janelia-experimental-technology/FlySong/miniFlySong/miniFlySong Rig.jpg

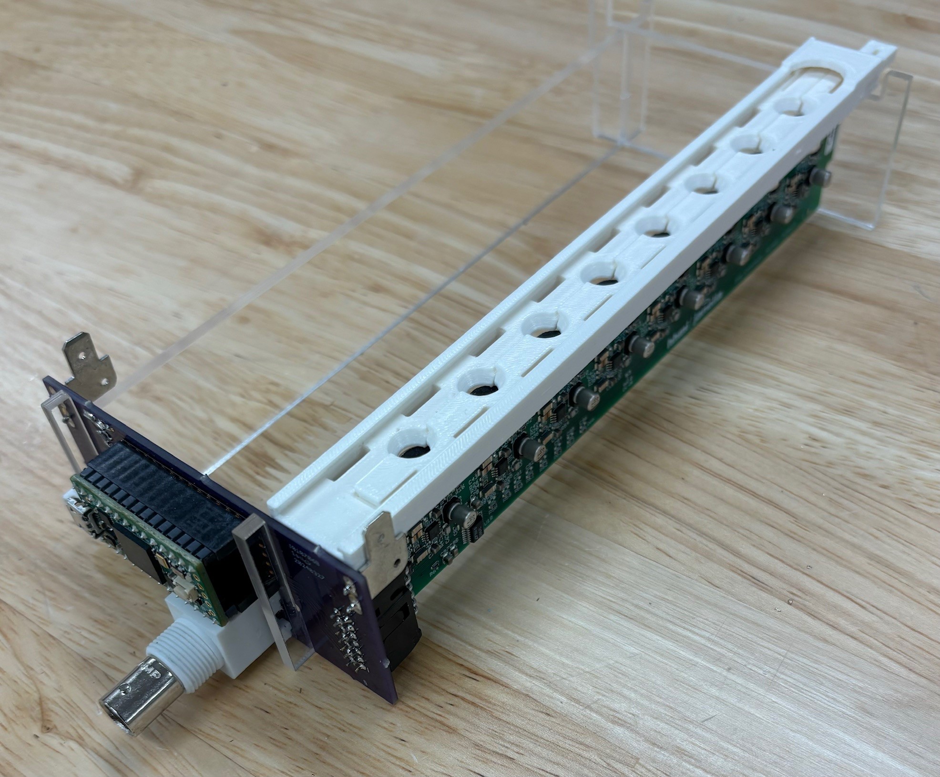
miniFlySong/miniFlySong Rig.jpg
