janelia-experimental-technology/FlySong/PHOTOS/camera cables.jpg

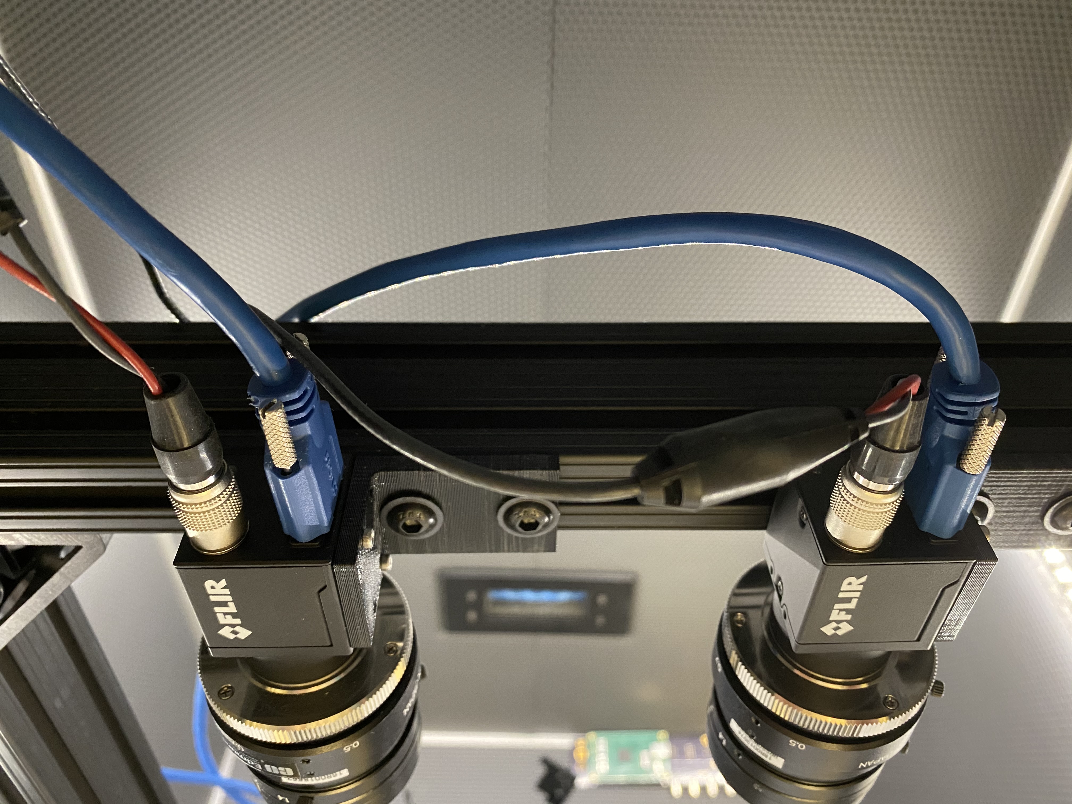
PHOTOS/camera cables.jpg
