janelia-experimental-technology/FlySong/PHOTOS/cameras and mount.jpg

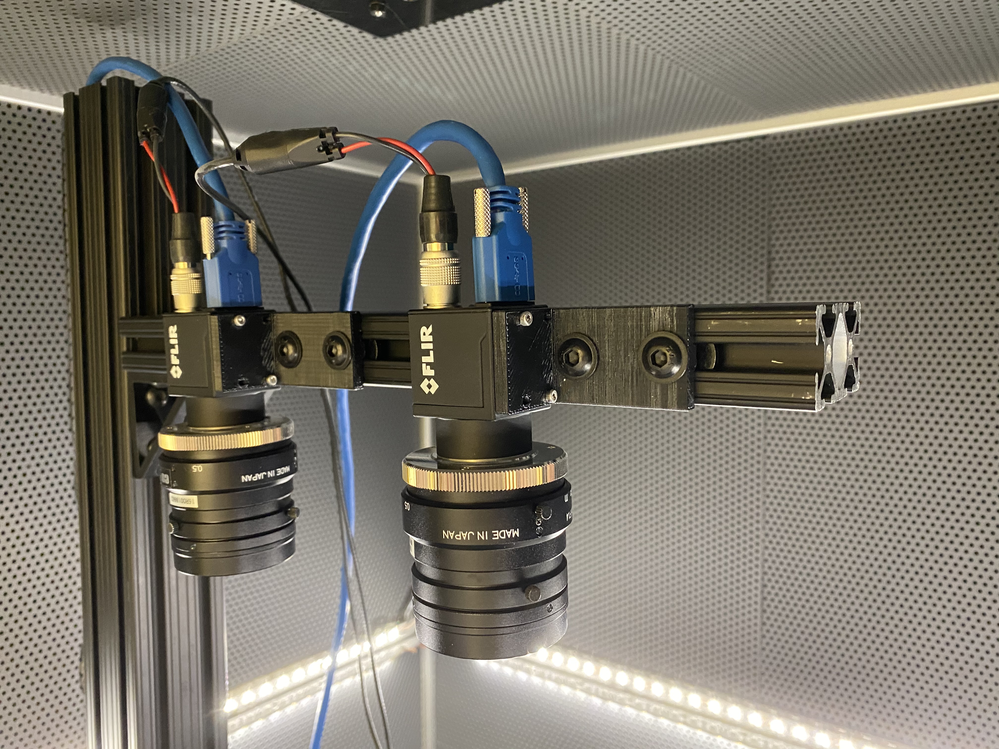
PHOTOS/cameras and mount.jpg
