janelia-experimental-technology/FlySong/PHOTOS/cameras.jpg

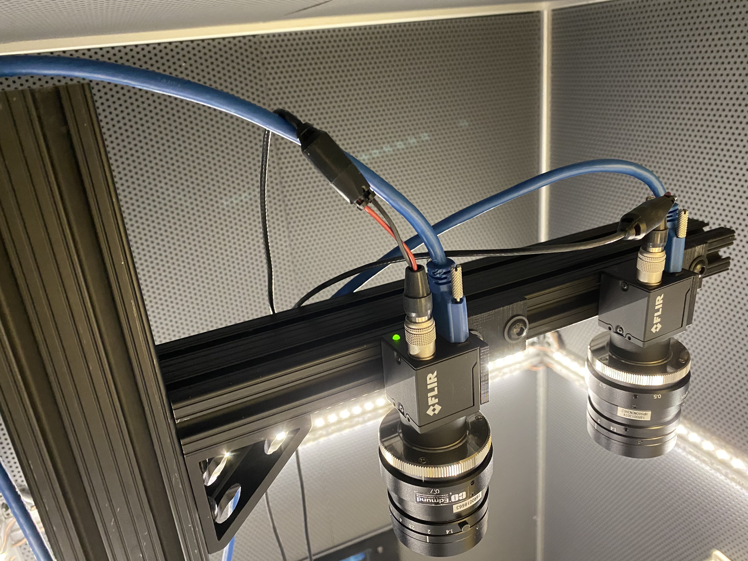
PHOTOS/cameras.jpg
