janelia-experimental-technology/FlySong/PHOTOS/RIG WITH RGB/Drigwithfrontmirror.jpg

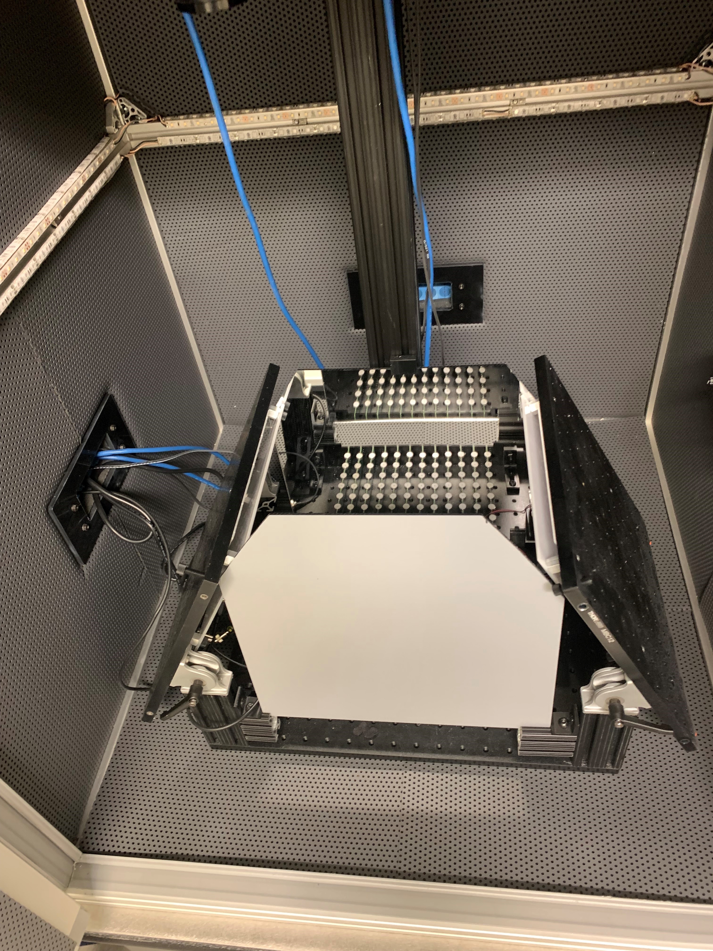
PHOTOS/RIG WITH RGB/Drigwithfrontmirror.jpg
