janelia-experimental-technology/FlySong/PHOTOS/RIG WITH RGB/LEDrigbehind.jpg

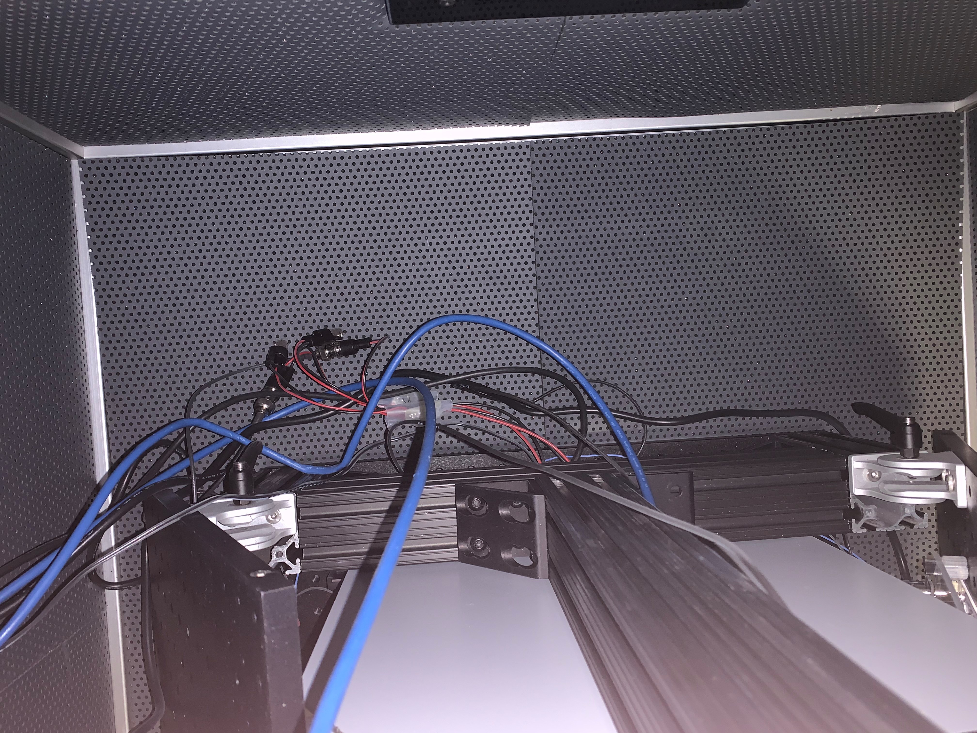
PHOTOS/RIG WITH RGB/LEDrigbehind.jpg
