janelia-experimental-technology/FlySong/PHOTOS/RIG WITH RGB/LEDrigtop2.jpg

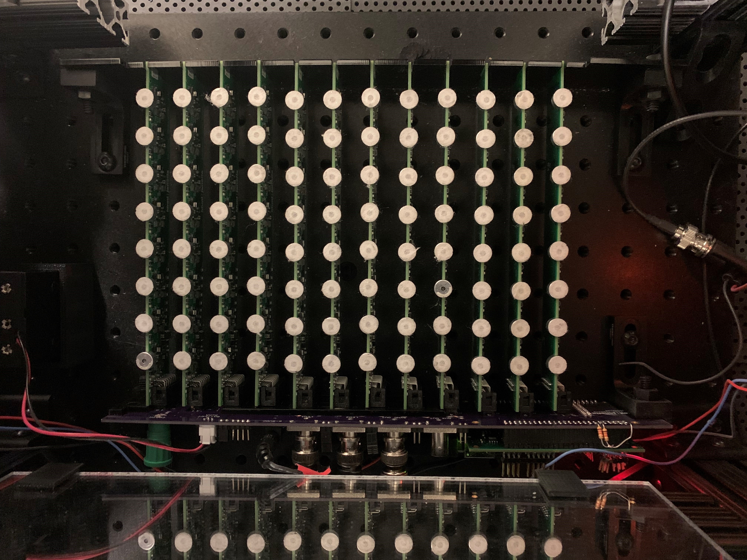
PHOTOS/RIG WITH RGB/LEDrigtop2.jpg
