janelia-experimental-technology/FlySong/PHOTOS/RIG WITH RGB/LEDrigtop.jpg

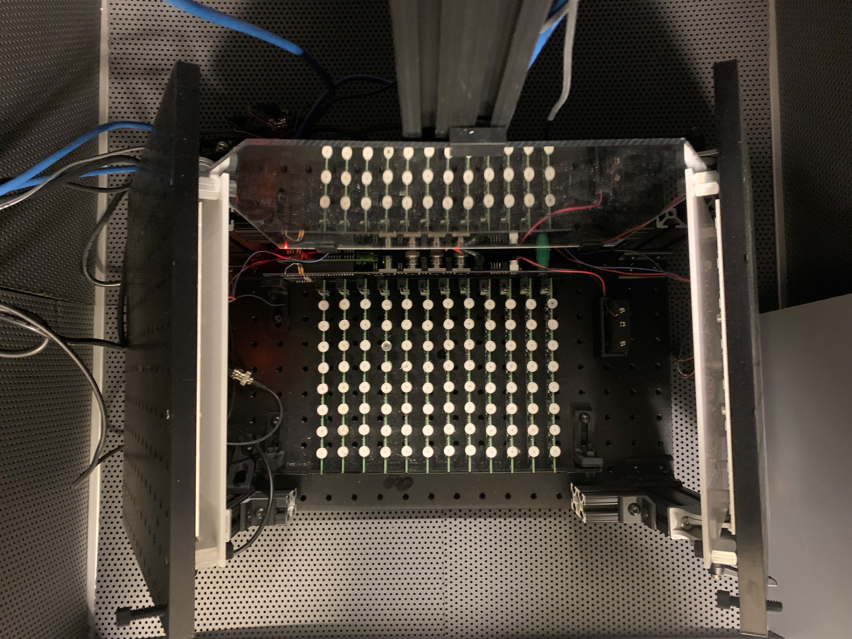
PHOTOS/RIG WITH RGB/LEDrigtop.jpg
