janelia-experimental-technology/FlySong/PHOTOS/Single mic board.JPG

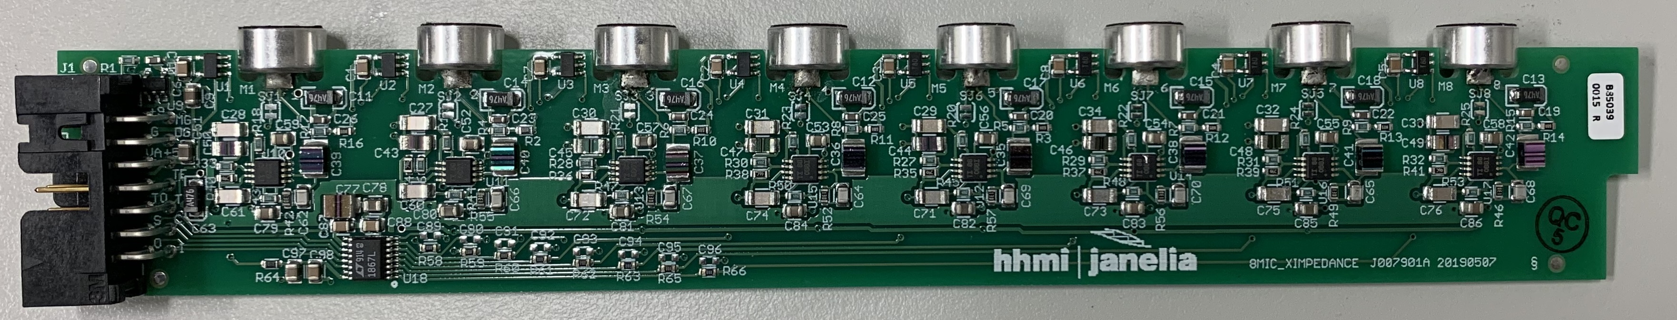
PHOTOS/Single mic board.JPG
