janelia-experimental-technology/FlySong/Mechanical/LaserCuts/ChamberSupports_LaserCuts_J008340A.dxf

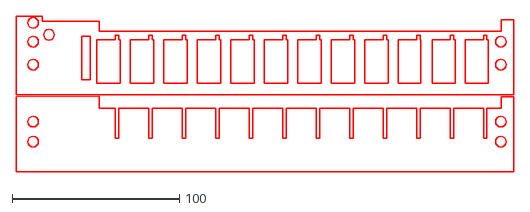
[picture p31: CAD file, 2023-11-08]
Mechanical/LaserCuts/ChamberSupports_LaserCuts_J008340A.dxf
297.0 x 93.0
