janelia-experimental-technology/FlySong/Electrical/TriggerCable.pdf

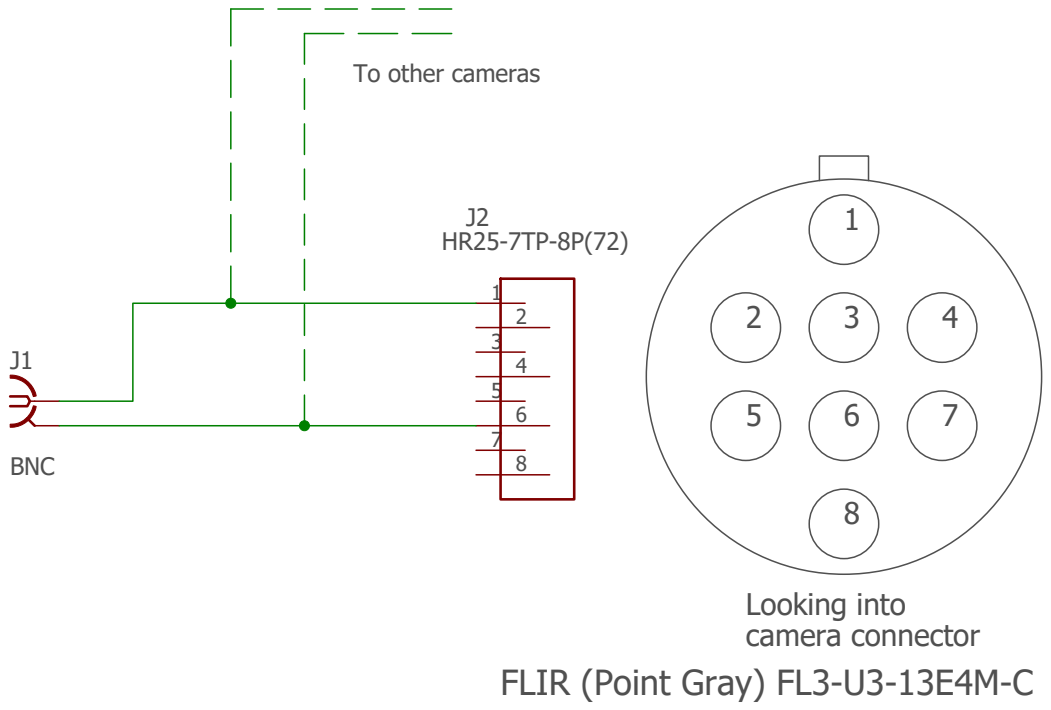
[picture p32: page 1]
Looking into camera connector; BNC; Date: not saved!; Sheet: 1/1; REV:; TITLE:; Document Number:; TriggerCable

To other cameras

FLIR (Point Gray) FL3-U3-13E4M-C
