janelia-experimental-technology/FlySong/FPGAsource/FPGAwSRAM/FPGAwSRAM.srcs/sources_1/imports/96mic/okBTPipeIn.v

// Copyright 1986-2015 Xilinx, Inc. All Rights Reserved.
// --------------------------------------------------------------------------------
// Tool Version: Vivado v.2015.1 (win64) Build 1215546 Mon Apr 27 19:22:08 MDT 2015
// Date        : Mon Mar 14 14:44:02 2016
// Host        : ENG001 running 64-bit major release  (build 9200)
// Command     : write_verilog encrypted/okBTPipeIn.v -force
// Design      : okBTPipeIn
// Purpose     : This is a Verilog netlist of the current design or from a specific cell of the design. The output is an
//               IEEE 1364-2001 compliant Verilog HDL file that contains netlist information obtained from the input
//               design files.
// Device      : xc7a15tftg256-1
// --------------------------------------------------------------------------------
`timescale 1 ps / 1 ps
`pragma protect begin_protected
`pragma protect version = 1
`pragma protect encrypt_agent = "XILINX"
`pragma protect encrypt_agent_info = "Xilinx Encryption Tool 2014"
`pragma protect key_keyowner = "Xilinx", key_keyname= "xilinx_rsa_key", key_method = "rsa"
`pragma protect encoding = (enctype = "BASE64", line_length = 76, bytes = 256)
`pragma protect key_block
Fh4uwRzu/dnt5r1QK762rHFgJkB9yfB/yrZYcW5Xy1imGTabUug4dFeSXXOdPlOcM7rrzuRp/h0H
xBfA3tb1mhHGhxead6KLwcbITD29SkVixk7EAfrhfXsD7AJevRaIbT9SvUi80ju3tSvxARpVkpB9
lUH7NHTmvPrGc9fxVg5305HHPtw7yxeQ5QIUJT7Pp70OrIjOF14pLfanrSt3Sp5aoSveh1QaKLCC
TkiL7rNUEZyYnwcvnaIB3q99gLVUxVYKGOKqI85L7sqMW/h4TQZ/COntCu+Ya/B+OVFPVO0xWF26
eNhhSwdBffT30fBPmPcC9+IbmshED+ESR4J4xw==

`pragma protect data_method = "AES128-CBC"
`pragma protect encoding = (enctype = "BASE64", line_length = 76, bytes = 5392)
`pragma protect data_block
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
`pragma protect end_protected
