janelia-experimental-technology/FlySong/FPGAsource/FPGAwSRAM/FPGAwSRAM.srcs/sources_1/imports/96mic/okBTPipeOut.v

// Copyright 1986-2015 Xilinx, Inc. All Rights Reserved.
// --------------------------------------------------------------------------------
// Tool Version: Vivado v.2015.1 (win64) Build 1215546 Mon Apr 27 19:22:08 MDT 2015
// Date        : Mon Mar 14 14:44:09 2016
// Host        : ENG001 running 64-bit major release  (build 9200)
// Command     : write_verilog encrypted/okBTPipeOut.v -force
// Design      : okBTPipeOut
// Purpose     : This is a Verilog netlist of the current design or from a specific cell of the design. The output is an
//               IEEE 1364-2001 compliant Verilog HDL file that contains netlist information obtained from the input
//               design files.
// Device      : xc7a15tftg256-1
// --------------------------------------------------------------------------------
`timescale 1 ps / 1 ps
`pragma protect begin_protected
`pragma protect version = 1
`pragma protect encrypt_agent = "XILINX"
`pragma protect encrypt_agent_info = "Xilinx Encryption Tool 2014"
`pragma protect key_keyowner = "Xilinx", key_keyname= "xilinx_rsa_key", key_method = "rsa"
`pragma protect encoding = (enctype = "BASE64", line_length = 76, bytes = 256)
`pragma protect key_block
ceNoom6rbxBo+aYj+vBCbk7ZTXtGGbR1PNspMmEgzM12jxUhxhG8qXBXLPctP1Fa2NEXUIKIj4sh
Lmk7Nztbh1N6vVtappy26EiW4+ZoatkzdjAM5lZ5qNvalbiQNZPtWkysVhgkzsw+Dp858GLCppmi
96nc9nbWnJmwm5MVFI5jCu1HGCWIx/ghrDwHuIKqzORi1j1ZawqX2oKo0zJgWOreHumBSc8EhQHg
zt+WDYfpjdkIg/9/9+zmKAe8qIX0/IW1a2M/NPYptsqt0FcJzw/kCYaHBI710mXWGc9dgOKZqzsU
7VkZgweg8jSlaVgsCk0Rwtsa72uSkHqy9gIMng==

`pragma protect data_method = "AES128-CBC"
`pragma protect encoding = (enctype = "BASE64", line_length = 76, bytes = 5536)
`pragma protect data_block
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
jU1PiOcMdw==
`pragma protect end_protected
