janelia-experimental-technology/FlySong/FPGAsource/FPGAwSRAM/FPGAwSRAM.srcs/sources_1/imports/96mic/okWireIn.v

// Copyright 1986-2015 Xilinx, Inc. All Rights Reserved.
// --------------------------------------------------------------------------------
// Tool Version: Vivado v.2015.1 (win64) Build 1215546 Mon Apr 27 19:22:08 MDT 2015
// Date        : Mon Mar 14 14:44:37 2016
// Host        : ENG001 running 64-bit major release  (build 9200)
// Command     : write_verilog encrypted/okWireIn.v -force
// Design      : okWireIn
// Purpose     : This is a Verilog netlist of the current design or from a specific cell of the design. The output is an
//               IEEE 1364-2001 compliant Verilog HDL file that contains netlist information obtained from the input
//               design files.
// Device      : xc7a15tftg256-1
// --------------------------------------------------------------------------------
`timescale 1 ps / 1 ps
`pragma protect begin_protected
`pragma protect version = 1
`pragma protect encrypt_agent = "XILINX"
`pragma protect encrypt_agent_info = "Xilinx Encryption Tool 2014"
`pragma protect key_keyowner = "Xilinx", key_keyname= "xilinx_rsa_key", key_method = "rsa"
`pragma protect encoding = (enctype = "BASE64", line_length = 76, bytes = 256)
`pragma protect key_block
He7n+UnxRlqTMnbJBcvT+3Ny8AGCD7760dxFaGgSg6jzVUlvq3/qnky7S4Cd0uXEhExU9A/G/+jV
swbCJDNCJwODO/1EqRvnPjltjimub9iz1Rq6a6vzJW6LPC6FEMTQgqMVCWjS6LJ6SVMqL0UyoaQ9
mJKnjG3gI8pImYNv0nE6eXMlkPftPxMJrk4+rkDeZ9FqTpFV0Z3isBoDvDqWVgWyZ18B3afR37E+
UQ2zCmuS6W7EVIW3SkF+OUdjV+bZebcOUz6w5B1g7iSEbGy5MXDnqL2yVPUtmJeCjpq6eEYTkNLz
hUoXTe+vTRjOGO54XuR7F+5prIaDBwPDYvPaow==

`pragma protect data_method = "AES128-CBC"
`pragma protect encoding = (enctype = "BASE64", line_length = 76, bytes = 6432)
`pragma protect data_block
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
`pragma protect end_protected
