janelia-experimental-technology/FlySong/FPGAsource/FPGAwSRAM/FPGAwSRAM.srcs/sources_1/imports/96mic/okWireOut.v

// Copyright 1986-2015 Xilinx, Inc. All Rights Reserved.
// --------------------------------------------------------------------------------
// Tool Version: Vivado v.2015.1 (win64) Build 1215546 Mon Apr 27 19:22:08 MDT 2015
// Date        : Mon Mar 14 14:44:42 2016
// Host        : ENG001 running 64-bit major release  (build 9200)
// Command     : write_verilog encrypted/okWireOut.v -force
// Design      : okWireOut
// Purpose     : This is a Verilog netlist of the current design or from a specific cell of the design. The output is an
//               IEEE 1364-2001 compliant Verilog HDL file that contains netlist information obtained from the input
//               design files.
// Device      : xc7a15tftg256-1
// --------------------------------------------------------------------------------
`timescale 1 ps / 1 ps
`pragma protect begin_protected
`pragma protect version = 1
`pragma protect encrypt_agent = "XILINX"
`pragma protect encrypt_agent_info = "Xilinx Encryption Tool 2014"
`pragma protect key_keyowner = "Xilinx", key_keyname= "xilinx_rsa_key", key_method = "rsa"
`pragma protect encoding = (enctype = "BASE64", line_length = 76, bytes = 256)
`pragma protect key_block
GboD47aqS2xv7i+Mjs8w+c63W4jbrSMpvLNoYOUUPcw50pbawmT7ps6S/S+g/cNI58UlBlEwAhK+
Sx8hgtqBs2+CmGYano4VyTPCSOqxhMlZyD30jkmOnLEsLR1ohXVEG1MTq1i9gegkzCn3vler0AEI
fUjtMy9CUX/hyDeYu13k7a/5+pmBYDl36X6wqfOnrReti4ec2RCOsUijL1nqEvBkIYPvCQ8H3fgh
JNvdqz3dfRVaCAJR0bVbRj0W6pX6Rpyt5IuMZQDwBusYJdi9ITpmQrkOWyst0UhkvwzftG4AZWUk
JdzQSXtuBW/FiY+xsNkyG4v9nht3/ebLZBd5pw==

`pragma protect data_method = "AES128-CBC"
`pragma protect encoding = (enctype = "BASE64", line_length = 76, bytes = 7312)
`pragma protect data_block
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
nPi3865pbc2lOAc/o1ByMg==
`pragma protect end_protected
