janelia-experimental-technology/FlySong/FPGAsource/FPGAwSRAM/FPGAwSRAM.srcs/sources_1/imports/96mic/okPipeIn.v

// Copyright 1986-2015 Xilinx, Inc. All Rights Reserved.
// --------------------------------------------------------------------------------
// Tool Version: Vivado v.2015.1 (win64) Build 1215546 Mon Apr 27 19:22:08 MDT 2015
// Date        : Mon Mar 14 14:44:14 2016
// Host        : ENG001 running 64-bit major release  (build 9200)
// Command     : write_verilog encrypted/okPipeIn.v -force
// Design      : okPipeIn
// Purpose     : This is a Verilog netlist of the current design or from a specific cell of the design. The output is an
//               IEEE 1364-2001 compliant Verilog HDL file that contains netlist information obtained from the input
//               design files.
// Device      : xc7a15tftg256-1
// --------------------------------------------------------------------------------
`timescale 1 ps / 1 ps
`pragma protect begin_protected
`pragma protect version = 1
`pragma protect encrypt_agent = "XILINX"
`pragma protect encrypt_agent_info = "Xilinx Encryption Tool 2014"
`pragma protect key_keyowner = "Xilinx", key_keyname= "xilinx_rsa_key", key_method = "rsa"
`pragma protect encoding = (enctype = "BASE64", line_length = 76, bytes = 256)
`pragma protect key_block
pp8uegFR+HcuxO82qfOr/bnWbU4BhkaXkdLwH8kbdE8cu3OBB891qpwMdlxpvV5KDxcGkOC8xI/2
yNy2IJ7eNr5S63N6x7KBeUN9nIWkN0+dvoPAUmtxsJJoLDsxoXaWtQ4/IgyaOjxGWN6gyyeIDGrU
1cCZfWLVN4PrGTT/yPVN+qkrLAM5fl4r45IIvLfLcIgTlLmg++MvKfiQiGMb1EWrXBI44qlEK90J
ciomIXwNng8LNQpz8hEPLRzbMAh2QkQs/O+8VBsz8lPHCuIh1Q07/nGMN1V7noRKYraVMqKKY4C4
T+oO5eQox+KOT7l24IIg/glWMKQTSW2mFGHPIA==

`pragma protect data_method = "AES128-CBC"
`pragma protect encoding = (enctype = "BASE64", line_length = 76, bytes = 5328)
`pragma protect data_block
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
GgHhEjmCwbM9kBYY49kCXhUT7aydmYbmcKWH
`pragma protect end_protected
