janelia-experimental-technology/FlySong/FPGAsource/FPGAwSRAM/FPGAwSRAM.srcs/sources_1/imports/96mic/okPipeOut.v

// Copyright 1986-2015 Xilinx, Inc. All Rights Reserved.
// --------------------------------------------------------------------------------
// Tool Version: Vivado v.2015.1 (win64) Build 1215546 Mon Apr 27 19:22:08 MDT 2015
// Date        : Mon Mar 14 14:44:20 2016
// Host        : ENG001 running 64-bit major release  (build 9200)
// Command     : write_verilog encrypted/okPipeOut.v -force
// Design      : okPipeOut
// Purpose     : This is a Verilog netlist of the current design or from a specific cell of the design. The output is an
//               IEEE 1364-2001 compliant Verilog HDL file that contains netlist information obtained from the input
//               design files.
// Device      : xc7a15tftg256-1
// --------------------------------------------------------------------------------
`timescale 1 ps / 1 ps
`pragma protect begin_protected
`pragma protect version = 1
`pragma protect encrypt_agent = "XILINX"
`pragma protect encrypt_agent_info = "Xilinx Encryption Tool 2014"
`pragma protect key_keyowner = "Xilinx", key_keyname= "xilinx_rsa_key", key_method = "rsa"
`pragma protect encoding = (enctype = "BASE64", line_length = 76, bytes = 256)
`pragma protect key_block
BsgjUAD1O8euvel2hbkc8te3elD8HtfBgAa/XrN2xeB4rmm7DSoyeXS7/2h3a5ISqn9xaWsTo34h
6ck4zlRUcANFHBE36Xael0QoKT0daD75NywGKJIlfdfcsdZKJtPPEIldq0FoRchDVK1zKBIiD75I
3qChKLhP5L/AFR94uIm7hYtUpP0WqRznH39JVAd4cqw62go1rKzbpY8ZdBWE3UNPiBGsLxv5KSGj
NnaTXdPe6cxQgYOdlAtetth9hKQe7eGvcKOSGFE03r1zPMe3xlX4PIDCqFE/+adAgG0R84cW+xgS
fgf8NICXgJ64PibA/IK8HKZ6+rSC9EmyGeb36A==

`pragma protect data_method = "AES128-CBC"
`pragma protect encoding = (enctype = "BASE64", line_length = 76, bytes = 5232)
`pragma protect data_block
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
`pragma protect end_protected
