janelia-experimental-technology/FlySong/FPGAsource/FPGAwSRAM/.Xil/FPGAwSRAM.ip_user_files/ip/mult_gen_0/mult_gen_0_stub.v

// Copyright 1986-2017 Xilinx, Inc. All Rights Reserved.
// --------------------------------------------------------------------------------
// Tool Version: Vivado v.2017.1 (win64) Build 1846317 Fri Apr 14 18:55:03 MDT 2017
// Date        : Sun May 14 15:34:09 2017
// Host        : sawtelles-lw1 running 64-bit major release  (build 9200)
// Command     : write_verilog -force -mode synth_stub
//               C:/PROJECTS/STERN/96CH_RECORDER/FPGA/96mic/96mic.runs/mult_gen_0_synth_1/mult_gen_0_stub.v
// Design      : mult_gen_0
// Purpose     : Stub declaration of top-level module interface
// Device      : xc7a15tftg256-1
// --------------------------------------------------------------------------------

// This empty module with port declaration file causes synthesis tools to infer a black box for IP.
// The synthesis directives are for Synopsys Synplify support to prevent IO buffer insertion.
// Please paste the declaration into a Verilog source file or add the file as an additional source.
(* x_core_info = "mult_gen_v12_0_12,Vivado 2017.1" *)
module mult_gen_0(CLK, A, P)
/* synthesis syn_black_box black_box_pad_pin="CLK,A[15:0],P[32:0]" */;
  input CLK;
  input [15:0]A;
  output [32:0]P;
endmodule
