janelia-experimental-technology/FlySong/FPGAsource/FPGAwSRAM/.Xil/FPGAwSRAM.ip_user_files/ip/mult_gen_0/mult_gen_0_stub.vhdl

-- Copyright 1986-2017 Xilinx, Inc. All Rights Reserved.
-- --------------------------------------------------------------------------------
-- Tool Version: Vivado v.2017.1 (win64) Build 1846317 Fri Apr 14 18:55:03 MDT 2017
-- Date        : Sun May 14 15:34:09 2017
-- Host        : sawtelles-lw1 running 64-bit major release  (build 9200)
-- Command     : write_vhdl -force -mode synth_stub
--               C:/PROJECTS/STERN/96CH_RECORDER/FPGA/96mic/96mic.runs/mult_gen_0_synth_1/mult_gen_0_stub.vhdl
-- Design      : mult_gen_0
-- Purpose     : Stub declaration of top-level module interface
-- Device      : xc7a15tftg256-1
-- --------------------------------------------------------------------------------
library IEEE;
use IEEE.STD_LOGIC_1164.ALL;

entity mult_gen_0 is
  Port ( 
    CLK : in STD_LOGIC;
    A : in STD_LOGIC_VECTOR ( 15 downto 0 );
    P : out STD_LOGIC_VECTOR ( 32 downto 0 )
  );

end mult_gen_0;

architecture stub of mult_gen_0 is
attribute syn_black_box : boolean;
attribute black_box_pad_pin : string;
attribute syn_black_box of stub : architecture is true;
attribute black_box_pad_pin of stub : architecture is "CLK,A[15:0],P[32:0]";
attribute x_core_info : string;
attribute x_core_info of stub : architecture is "mult_gen_v12_0_12,Vivado 2017.1";
begin
end;
