janelia-experimental-technology/FlySong/FPGAsource/FPGAwSRAM/.Xil/FPGAwSRAM.ip_user_files/ip/mult_gen_0/mult_gen_0_sim_netlist.v

// Copyright 1986-2017 Xilinx, Inc. All Rights Reserved.
// --------------------------------------------------------------------------------
// Tool Version: Vivado v.2017.1 (win64) Build 1846317 Fri Apr 14 18:55:03 MDT 2017
// Date        : Sun May 14 15:34:09 2017
// Host        : sawtelles-lw1 running 64-bit major release  (build 9200)
// Command     : write_verilog -force -mode funcsim
//               C:/PROJECTS/STERN/96CH_RECORDER/FPGA/96mic/96mic.runs/mult_gen_0_synth_1/mult_gen_0_sim_netlist.v
// Design      : mult_gen_0
// Purpose     : This verilog netlist is a functional simulation representation of the design and should not be modified
//               or synthesized. This netlist cannot be used for SDF annotated simulation.
// Device      : xc7a15tftg256-1
// --------------------------------------------------------------------------------
`timescale 1 ps / 1 ps

(* CHECK_LICENSE_TYPE = "mult_gen_0,mult_gen_v12_0_12,{}" *) (* downgradeipidentifiedwarnings = "yes" *) (* x_core_info = "mult_gen_v12_0_12,Vivado 2017.1" *) 
(* NotValidForBitStream *)
module mult_gen_0
   (CLK,
    A,
    P);
  (* x_interface_info = "xilinx.com:signal:clock:1.0 clk_intf CLK" *) input CLK;
  (* x_interface_info = "xilinx.com:signal:data:1.0 a_intf DATA" *) input [15:0]A;
  (* x_interface_info = "xilinx.com:signal:data:1.0 p_intf DATA" *) output [32:0]P;

  wire [15:0]A;
  wire CLK;
  wire [32:0]P;
  wire [47:0]NLW_U0_PCASC_UNCONNECTED;
  wire [1:0]NLW_U0_ZERO_DETECT_UNCONNECTED;

  (* C_A_TYPE = "1" *) 
  (* C_A_WIDTH = "16" *) 
  (* C_B_TYPE = "1" *) 
  (* C_B_VALUE = "10010010101011100" *) 
  (* C_B_WIDTH = "17" *) 
  (* C_CCM_IMP = "2" *) 
  (* C_CE_OVERRIDES_SCLR = "0" *) 
  (* C_HAS_CE = "0" *) 
  (* C_HAS_SCLR = "0" *) 
  (* C_HAS_ZERO_DETECT = "0" *) 
  (* C_LATENCY = "1" *) 
  (* C_MODEL_TYPE = "0" *) 
  (* C_MULT_TYPE = "2" *) 
  (* C_OPTIMIZE_GOAL = "1" *) 
  (* C_OUT_HIGH = "32" *) 
  (* C_OUT_LOW = "0" *) 
  (* C_ROUND_OUTPUT = "0" *) 
  (* C_ROUND_PT = "0" *) 
  (* C_VERBOSITY = "0" *) 
  (* C_XDEVICEFAMILY = "artix7" *) 
  (* downgradeipidentifiedwarnings = "yes" *) 
  mult_gen_0_mult_gen_v12_0_12 U0
       (.A(A),
        .B({1'b0,1'b0,1'b0,1'b0,1'b0,1'b0,1'b0,1'b0,1'b0,1'b0,1'b0,1'b0,1'b0,1'b0,1'b0,1'b0,1'b0}),
        .CE(1'b1),
        .CLK(CLK),
        .P(P),
        .PCASC(NLW_U0_PCASC_UNCONNECTED[47:0]),
        .SCLR(1'b0),
        .ZERO_DETECT(NLW_U0_ZERO_DETECT_UNCONNECTED[1:0]));
endmodule

(* C_A_TYPE = "1" *) (* C_A_WIDTH = "16" *) (* C_B_TYPE = "1" *) 
(* C_B_VALUE = "10010010101011100" *) (* C_B_WIDTH = "17" *) (* C_CCM_IMP = "2" *) 
(* C_CE_OVERRIDES_SCLR = "0" *) (* C_HAS_CE = "0" *) (* C_HAS_SCLR = "0" *) 
(* C_HAS_ZERO_DETECT = "0" *) (* C_LATENCY = "1" *) (* C_MODEL_TYPE = "0" *) 
(* C_MULT_TYPE = "2" *) (* C_OPTIMIZE_GOAL = "1" *) (* C_OUT_HIGH = "32" *) 
(* C_OUT_LOW = "0" *) (* C_ROUND_OUTPUT = "0" *) (* C_ROUND_PT = "0" *) 
(* C_VERBOSITY = "0" *) (* C_XDEVICEFAMILY = "artix7" *) (* ORIG_REF_NAME = "mult_gen_v12_0_12" *) 
(* downgradeipidentifiedwarnings = "yes" *) 
module mult_gen_0_mult_gen_v12_0_12
   (CLK,
    A,
    B,
    CE,
    SCLR,
    ZERO_DETECT,
    P,
    PCASC);
  input CLK;
  input [15:0]A;
  input [16:0]B;
  input CE;
  input SCLR;
  output [1:0]ZERO_DETECT;
  output [32:0]P;
  output [47:0]PCASC;

  wire \<const0> ;
  wire [15:0]A;
  wire CLK;
  wire [32:2]\^P ;
  wire [1:0]NLW_i_mult_P_UNCONNECTED;
  wire [47:0]NLW_i_mult_PCASC_UNCONNECTED;
  wire [1:0]NLW_i_mult_ZERO_DETECT_UNCONNECTED;

  assign P[32:2] = \^P [32:2];
  assign P[1] = \<const0> ;
  assign P[0] = \<const0> ;
  assign PCASC[47] = \<const0> ;
  assign PCASC[46] = \<const0> ;
  assign PCASC[45] = \<const0> ;
  assign PCASC[44] = \<const0> ;
  assign PCASC[43] = \<const0> ;
  assign PCASC[42] = \<const0> ;
  assign PCASC[41] = \<const0> ;
  assign PCASC[40] = \<const0> ;
  assign PCASC[39] = \<const0> ;
  assign PCASC[38] = \<const0> ;
  assign PCASC[37] = \<const0> ;
  assign PCASC[36] = \<const0> ;
  assign PCASC[35] = \<const0> ;
  assign PCASC[34] = \<const0> ;
  assign PCASC[33] = \<const0> ;
  assign PCASC[32] = \<const0> ;
  assign PCASC[31] = \<const0> ;
  assign PCASC[30] = \<const0> ;
  assign PCASC[29] = \<const0> ;
  assign PCASC[28] = \<const0> ;
  assign PCASC[27] = \<const0> ;
  assign PCASC[26] = \<const0> ;
  assign PCASC[25] = \<const0> ;
  assign PCASC[24] = \<const0> ;
  assign PCASC[23] = \<const0> ;
  assign PCASC[22] = \<const0> ;
  assign PCASC[21] = \<const0> ;
  assign PCASC[20] = \<const0> ;
  assign PCASC[19] = \<const0> ;
  assign PCASC[18] = \<const0> ;
  assign PCASC[17] = \<const0> ;
  assign PCASC[16] = \<const0> ;
  assign PCASC[15] = \<const0> ;
  assign PCASC[14] = \<const0> ;
  assign PCASC[13] = \<const0> ;
  assign PCASC[12] = \<const0> ;
  assign PCASC[11] = \<const0> ;
  assign PCASC[10] = \<const0> ;
  assign PCASC[9] = \<const0> ;
  assign PCASC[8] = \<const0> ;
  assign PCASC[7] = \<const0> ;
  assign PCASC[6] = \<const0> ;
  assign PCASC[5] = \<const0> ;
  assign PCASC[4] = \<const0> ;
  assign PCASC[3] = \<const0> ;
  assign PCASC[2] = \<const0> ;
  assign PCASC[1] = \<const0> ;
  assign PCASC[0] = \<const0> ;
  assign ZERO_DETECT[1] = \<const0> ;
  assign ZERO_DETECT[0] = \<const0> ;
  GND GND
       (.G(\<const0> ));
  (* C_A_TYPE = "1" *) 
  (* C_A_WIDTH = "16" *) 
  (* C_B_TYPE = "1" *) 
  (* C_B_VALUE = "10010010101011100" *) 
  (* C_B_WIDTH = "17" *) 
  (* C_CCM_IMP = "2" *) 
  (* C_CE_OVERRIDES_SCLR = "0" *) 
  (* C_HAS_CE = "0" *) 
  (* C_HAS_SCLR = "0" *) 
  (* C_HAS_ZERO_DETECT = "0" *) 
  (* C_LATENCY = "1" *) 
  (* C_MODEL_TYPE = "0" *) 
  (* C_MULT_TYPE = "2" *) 
  (* C_OPTIMIZE_GOAL = "1" *) 
  (* C_OUT_HIGH = "32" *) 
  (* C_OUT_LOW = "0" *) 
  (* C_ROUND_OUTPUT = "0" *) 
  (* C_ROUND_PT = "0" *) 
  (* C_VERBOSITY = "0" *) 
  (* C_XDEVICEFAMILY = "artix7" *) 
  (* downgradeipidentifiedwarnings = "yes" *) 
  mult_gen_0_mult_gen_v12_0_12_viv i_mult
       (.A(A),
        .B({1'b0,1'b0,1'b0,1'b0,1'b0,1'b0,1'b0,1'b0,1'b0,1'b0,1'b0,1'b0,1'b0,1'b0,1'b0,1'b0,1'b0}),
        .CE(1'b0),
        .CLK(CLK),
        .P({\^P ,NLW_i_mult_P_UNCONNECTED[1:0]}),
        .PCASC(NLW_i_mult_PCASC_UNCONNECTED[47:0]),
        .SCLR(1'b0),
        .ZERO_DETECT(NLW_i_mult_ZERO_DETECT_UNCONNECTED[1:0]));
endmodule
`pragma protect begin_protected
`pragma protect version = 1
`pragma protect encrypt_agent = "XILINX"
`pragma protect encrypt_agent_info = "Xilinx Encryption Tool 2015"
`pragma protect key_keyowner="Cadence Design Systems.", key_keyname="cds_rsa_key", key_method="rsa"
`pragma protect encoding = (enctype="BASE64", line_length=76, bytes=64)
`pragma protect key_block
hYn4T1Tz8lmB8loeGYuHmgEJp5TdMkRKn5tdK0Pxo3wkkBR/aG2es4RXT0Kx9IkGgy2jVWVPoeKB
usRl+M6Pxw==

`pragma protect key_keyowner="Mentor Graphics Corporation", key_keyname="MGC-VERIF-SIM-RSA-1", key_method="rsa"
`pragma protect encoding = (enctype="BASE64", line_length=76, bytes=128)
`pragma protect key_block
cZOTsELKZdXMGraSgAw9rgqxvSLbW0aT2lTeYBbmmRdIiILVX40Q3XF89sXvrmWq2q7dAJSXvpsX
1JIpxbCUMi40Nuru7hdg9WkNNMs1Q8UJCou9g/GNLxJnh56Wx2JqOiplBqlgeaLjd0T16sGmIYm4
kTNGsNPOASR/dWaldsE=

`pragma protect key_keyowner="Synopsys", key_keyname="SNPS-VCS-RSA-1", key_method="rsa"
`pragma protect encoding = (enctype="BASE64", line_length=76, bytes=128)
`pragma protect key_block
o6ehD67QiTZFs1auOjL5nkbDEbn3neiXmbyTqqoQKK+v0TaPL6hSxGHE/Fz3NtmR3RIza9+Y9rVH
Je7RNuyq8vsgofAGK5Qpf28P/9kF6eDh0JgLJHOonk7lnG+gufS3pMHIfioCEe/2wyoIxzbwUPNl
TCIJtbzDvWpcCIKBgiQ=

`pragma protect key_keyowner="Aldec", key_keyname="ALDEC15_001", key_method="rsa"
`pragma protect encoding = (enctype="BASE64", line_length=76, bytes=256)
`pragma protect key_block
cASOe3RHelXhU6s/jEEqAnadTjmj4ihjbMuYb8YjKT8lAROht6xaHEt/3WXUlUPXIpDwtJlexClV
csQVUSlNShzZmxBI5epxH/HJqLhQYwkRDFK2BUAagxn++cS1iWJGlow9Gha0EU+PfllVje3OWy4O
LbiqHgQlEG6sIGo0ZCj6KPC87SBAytHtAiVRpovpGAxLS/DLeXSJaavSSwOc7nmWFDaNEi9dJS9i
qixZxDI5QNaDp3uaBFLzKqo9oSPgNj1mYKRZp6XL0ganfqQCHh/snCyymi+o0DC5vSM/+RtCZHXA
A1u3UsiXv/IfegAneXJ/yU2Rpj4P9iaLKgmtjQ==

`pragma protect key_keyowner="ATRENTA", key_keyname="ATR-SG-2015-RSA-3", key_method="rsa"
`pragma protect encoding = (enctype="BASE64", line_length=76, bytes=256)
`pragma protect key_block
kAlIhoAHksCGo5mF85FXcP0dM1NExLuDn6ZkyfgoWH09b5qcw8bLJnQMlkLvdLRrczznUPKBLrRR
nUHSMi9UTzRZ0rrnazgGnHFEV1vyoRgDQDOpkZbrkgl/VynbkoMBhCQXYT59yyHhqjI6WeIYVipR
zyn+NdmUB+/GwlsSYygywX31rotvUxb4RZmCqg+UCemw+N0tS43QuIzJuG1JM+3+SVbU3LuVcClf
rOwWqAFHsOXBSrXNoPX6QeNlYUKy8gcjiaQqPSrbrSJWdgvqshdNnvLWuzkREOLY43TCoAFwM8p5
73h2VUHmwffIqzCELbp3Tee5sQXgMbvJ+Mbfpg==

`pragma protect key_keyowner="Xilinx", key_keyname="xilinx_2016_05", key_method="rsa"
`pragma protect encoding = (enctype="BASE64", line_length=76, bytes=256)
`pragma protect key_block
CFQ8408huN9E8h2/r246qkePkogHtf4rd5gf8GO4NiUzetOQ2my8cbvxYBjZy3yQSw0/LrN95Drj
cc3uAe9r+wOvBQ3aM7AKnKpRkAvmqyCRt8lkW5NRi37udLv8jQJ5gVByTJ76KIn8s2kfj/iHou8+
VyK641fcvp2Fk/dmC13HALsHzGvO1m9Kg3zHT1aJxtdh2FDGLhOy/TtcAEbSWUhNkclp4pw4r97T
urhhIiarPZZDEkAXG1Ezi9I9ebmvdHMRRa/e9P95Xg7vwS04EHfmVTpFKF7UHncoI46I8za8vjyZ
8MCKLS5zKbgCU1OCJ9lQ6mJX1roD79pJrnKYpw==

`pragma protect key_keyowner="Mentor Graphics Corporation", key_keyname="MGC-PREC-RSA", key_method="rsa"
`pragma protect encoding = (enctype="base64", line_length=76, bytes=256)
`pragma protect key_block
nAe2yz38W+toa47teXFomvr0s3S7B/mFs08V3isJo/x2QJRmzNs0XiNhAEvzTYJSpHgqTw5IzrWq
0lW2CNEVEn7nULmMZObrv1Tk/gy3nFeX8Ug9HLfX3V0QEmN2QZnRlPTpZ/jWElW/FsfAJoYrx5LJ
sIxZdHBH8mVP5RDmHVxEmHwOvzooeFGzyIdb2cq+TFJgYLtVUJmRxsBQHVlr+7TJ6IEHuExkLnjb
DyPnQFol/m9w7rcWk3cb/6sFXTI6YQplz5+kSyKpS7Lps3HnWjvnazi+2lVjikgzUvslX1TRa0yw
nUwudxo+/x26UMbNYdlsh2j/uG9z1Syvtox0FA==

`pragma protect key_keyowner="Synplicity", key_keyname="SYNP15_1", key_method="rsa"
`pragma protect encoding = (enctype="base64", line_length=76, bytes=256)
`pragma protect key_block
N1k8yedDzpZ6fllDD0pjuyFR32LIzWu0hurCyNGDLYa54A72Vtquyp8/YG/imGN8eUS3qaFAbnQt
HO+JvKbL3XRIMX0HLPbSykuJLWcdylfV1Ig2EkYNure4uqUqBnMyb1awePUmWo5YG3EYQav0b7Vv
UwgYmhz6w7jdE6Q9aGaXNOQU9fpNHWZzUzVmubb11BEUnG8ORR378OV0X6IsnfXAdL1sSiX7lnvr
D0R2q3Gm++FbV0Bvbpd8qIM7YczP8pd4/Bv+Z2oE/HbpBSP6cec+u7loIai9KZctbIUojEkj1xNK
mMOeQzY7zLn4YvBt5h6JrGzuRduJ9F2RqBWrbA==

`pragma protect data_method = "AES128-CBC"
`pragma protect encoding = (enctype = "BASE64", line_length = 76, bytes = 8464)
`pragma protect data_block
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
6BS+RbThDmCJME8frwk5gh5Wr9y0WFltS0nQHg==
`pragma protect end_protected
`ifndef GLBL
`define GLBL
`timescale  1 ps / 1 ps

module glbl ();

    parameter ROC_WIDTH = 100000;
    parameter TOC_WIDTH = 0;

//--------   STARTUP Globals --------------
    wire GSR;
    wire GTS;
    wire GWE;
    wire PRLD;
    tri1 p_up_tmp;
    tri (weak1, strong0) PLL_LOCKG = p_up_tmp;

    wire PROGB_GLBL;
    wire CCLKO_GLBL;
    wire FCSBO_GLBL;
    wire [3:0] DO_GLBL;
    wire [3:0] DI_GLBL;
   
    reg GSR_int;
    reg GTS_int;
    reg PRLD_int;

//--------   JTAG Globals --------------
    wire JTAG_TDO_GLBL;
    wire JTAG_TCK_GLBL;
    wire JTAG_TDI_GLBL;
    wire JTAG_TMS_GLBL;
    wire JTAG_TRST_GLBL;

    reg JTAG_CAPTURE_GLBL;
    reg JTAG_RESET_GLBL;
    reg JTAG_SHIFT_GLBL;
    reg JTAG_UPDATE_GLBL;
    reg JTAG_RUNTEST_GLBL;

    reg JTAG_SEL1_GLBL = 0;
    reg JTAG_SEL2_GLBL = 0 ;
    reg JTAG_SEL3_GLBL = 0;
    reg JTAG_SEL4_GLBL = 0;

    reg JTAG_USER_TDO1_GLBL = 1'bz;
    reg JTAG_USER_TDO2_GLBL = 1'bz;
    reg JTAG_USER_TDO3_GLBL = 1'bz;
    reg JTAG_USER_TDO4_GLBL = 1'bz;

    assign (strong1, weak0) GSR = GSR_int;
    assign (strong1, weak0) GTS = GTS_int;
    assign (weak1, weak0) PRLD = PRLD_int;

    initial begin
	GSR_int = 1'b1;
	PRLD_int = 1'b1;
	#(ROC_WIDTH)
	GSR_int = 1'b0;
	PRLD_int = 1'b0;
    end

    initial begin
	GTS_int = 1'b1;
	#(TOC_WIDTH)
	GTS_int = 1'b0;
    end

endmodule
`endif
