janelia-experimental-technology/FlySong/FPGAsource/FPGAwSRAM/.Xil/FPGAwSRAM.ip_user_files/ip/mult_gen_0/mult_gen_0_sim_netlist.vhdl

-- Copyright 1986-2017 Xilinx, Inc. All Rights Reserved.
-- --------------------------------------------------------------------------------
-- Tool Version: Vivado v.2017.1 (win64) Build 1846317 Fri Apr 14 18:55:03 MDT 2017
-- Date        : Sun May 14 15:34:09 2017
-- Host        : sawtelles-lw1 running 64-bit major release  (build 9200)
-- Command     : write_vhdl -force -mode funcsim
--               C:/PROJECTS/STERN/96CH_RECORDER/FPGA/96mic/96mic.runs/mult_gen_0_synth_1/mult_gen_0_sim_netlist.vhdl
-- Design      : mult_gen_0
-- Purpose     : This VHDL netlist is a functional simulation representation of the design and should not be modified or
--               synthesized. This netlist cannot be used for SDF annotated simulation.
-- Device      : xc7a15tftg256-1
-- --------------------------------------------------------------------------------
`protect begin_protected
`protect version = 1
`protect encrypt_agent = "XILINX"
`protect encrypt_agent_info = "Xilinx Encryption Tool 2015"
`protect key_keyowner="Cadence Design Systems.", key_keyname="cds_rsa_key", key_method="rsa"
`protect encoding = (enctype="BASE64", line_length=76, bytes=64)
`protect key_block
hYn4T1Tz8lmB8loeGYuHmgEJp5TdMkRKn5tdK0Pxo3wkkBR/aG2es4RXT0Kx9IkGgy2jVWVPoeKB
usRl+M6Pxw==

`protect key_keyowner="Mentor Graphics Corporation", key_keyname="MGC-VERIF-SIM-RSA-1", key_method="rsa"
`protect encoding = (enctype="BASE64", line_length=76, bytes=128)
`protect key_block
cZOTsELKZdXMGraSgAw9rgqxvSLbW0aT2lTeYBbmmRdIiILVX40Q3XF89sXvrmWq2q7dAJSXvpsX
1JIpxbCUMi40Nuru7hdg9WkNNMs1Q8UJCou9g/GNLxJnh56Wx2JqOiplBqlgeaLjd0T16sGmIYm4
kTNGsNPOASR/dWaldsE=

`protect key_keyowner="Synopsys", key_keyname="SNPS-VCS-RSA-1", key_method="rsa"
`protect encoding = (enctype="BASE64", line_length=76, bytes=128)
`protect key_block
o6ehD67QiTZFs1auOjL5nkbDEbn3neiXmbyTqqoQKK+v0TaPL6hSxGHE/Fz3NtmR3RIza9+Y9rVH
Je7RNuyq8vsgofAGK5Qpf28P/9kF6eDh0JgLJHOonk7lnG+gufS3pMHIfioCEe/2wyoIxzbwUPNl
TCIJtbzDvWpcCIKBgiQ=

`protect key_keyowner="Aldec", key_keyname="ALDEC15_001", key_method="rsa"
`protect encoding = (enctype="BASE64", line_length=76, bytes=256)
`protect key_block
cASOe3RHelXhU6s/jEEqAnadTjmj4ihjbMuYb8YjKT8lAROht6xaHEt/3WXUlUPXIpDwtJlexClV
csQVUSlNShzZmxBI5epxH/HJqLhQYwkRDFK2BUAagxn++cS1iWJGlow9Gha0EU+PfllVje3OWy4O
LbiqHgQlEG6sIGo0ZCj6KPC87SBAytHtAiVRpovpGAxLS/DLeXSJaavSSwOc7nmWFDaNEi9dJS9i
qixZxDI5QNaDp3uaBFLzKqo9oSPgNj1mYKRZp6XL0ganfqQCHh/snCyymi+o0DC5vSM/+RtCZHXA
A1u3UsiXv/IfegAneXJ/yU2Rpj4P9iaLKgmtjQ==

`protect key_keyowner="ATRENTA", key_keyname="ATR-SG-2015-RSA-3", key_method="rsa"
`protect encoding = (enctype="BASE64", line_length=76, bytes=256)
`protect key_block
kAlIhoAHksCGo5mF85FXcP0dM1NExLuDn6ZkyfgoWH09b5qcw8bLJnQMlkLvdLRrczznUPKBLrRR
nUHSMi9UTzRZ0rrnazgGnHFEV1vyoRgDQDOpkZbrkgl/VynbkoMBhCQXYT59yyHhqjI6WeIYVipR
zyn+NdmUB+/GwlsSYygywX31rotvUxb4RZmCqg+UCemw+N0tS43QuIzJuG1JM+3+SVbU3LuVcClf
rOwWqAFHsOXBSrXNoPX6QeNlYUKy8gcjiaQqPSrbrSJWdgvqshdNnvLWuzkREOLY43TCoAFwM8p5
73h2VUHmwffIqzCELbp3Tee5sQXgMbvJ+Mbfpg==

`protect key_keyowner="Xilinx", key_keyname="xilinx_2016_05", key_method="rsa"
`protect encoding = (enctype="BASE64", line_length=76, bytes=256)
`protect key_block
CFQ8408huN9E8h2/r246qkePkogHtf4rd5gf8GO4NiUzetOQ2my8cbvxYBjZy3yQSw0/LrN95Drj
cc3uAe9r+wOvBQ3aM7AKnKpRkAvmqyCRt8lkW5NRi37udLv8jQJ5gVByTJ76KIn8s2kfj/iHou8+
VyK641fcvp2Fk/dmC13HALsHzGvO1m9Kg3zHT1aJxtdh2FDGLhOy/TtcAEbSWUhNkclp4pw4r97T
urhhIiarPZZDEkAXG1Ezi9I9ebmvdHMRRa/e9P95Xg7vwS04EHfmVTpFKF7UHncoI46I8za8vjyZ
8MCKLS5zKbgCU1OCJ9lQ6mJX1roD79pJrnKYpw==

`protect key_keyowner="Mentor Graphics Corporation", key_keyname="MGC-PREC-RSA", key_method="rsa"
`protect encoding = (enctype="base64", line_length=76, bytes=256)
`protect key_block
jwEOFYbLuv/pGZXao/BmMSTKOV4eJLYGoyW5Pfe/4vnFCwwL2EF5fTZp6byqCw0jtUtIhI/OW4Gb
1v329NSw1nczBtur5BSMpsBZhNKBXKJ48MsCCqieWHJSsD0kbltheltU+3DKnpylOa3okJz9KBnN
B5F3B06+69EMSlGskkuYyH+vojYd+j/Dpi6i8PMfzBFr7PEeB68BKKW91mFvPDtRrFfNTJC3Z3Dx
HXoQ3bcLCYDVGOlaiQCmhtJ2hpvRfx12q52Nnr0ufhyt80THnInRY9sMppAnPSXtiQraCXqI5vI4
6DMNelbpP3yDNwDkKk0G9jEi3MM8F4t+0QwX1Q==

`protect key_keyowner="Synplicity", key_keyname="SYNP15_1", key_method="rsa"
`protect encoding = (enctype="base64", line_length=76, bytes=256)
`protect key_block
SxWPGgzeXpVxYfctVCGs7QnxlpRLkJoNRNVUBtSq1qXpth73c+VRx7rSVlE0nCudhwaFgbiwqaJh
/Het3M2y1LBcs840wmDVIQLPkhYbbG+9XUVFE8wzl2m4n3QXzBVvTDAFfZEP/7qqEUiNuJd6FiLF
UC05C8C3rdVwZq26N/v/d+yX/f/16X1CWq6r35y5ViObCBY6oKCP4xUHKmgHKCkDOlqAIh+txpP3
0mLn19HctPuu9g+pnt87yLY/yqXXoajfVizgFnynsiAclMEjFSpUa60HDGoJf7isEoBwpYJpo74/
XyiQGZgtvZL1qRvqZ/s4KvwcNpdvWHHto58X7w==

`protect data_method = "AES128-CBC"
`protect encoding = (enctype = "BASE64", line_length = 76, bytes = 11392)
`protect data_block
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
`protect end_protected
library IEEE;
use IEEE.STD_LOGIC_1164.ALL;
library UNISIM;
use UNISIM.VCOMPONENTS.ALL;
entity mult_gen_0_mult_gen_v12_0_12 is
  port (
    CLK : in STD_LOGIC;
    A : in STD_LOGIC_VECTOR ( 15 downto 0 );
    B : in STD_LOGIC_VECTOR ( 16 downto 0 );
    CE : in STD_LOGIC;
    SCLR : in STD_LOGIC;
    ZERO_DETECT : out STD_LOGIC_VECTOR ( 1 downto 0 );
    P : out STD_LOGIC_VECTOR ( 32 downto 0 );
    PCASC : out STD_LOGIC_VECTOR ( 47 downto 0 )
  );
  attribute C_A_TYPE : integer;
  attribute C_A_TYPE of mult_gen_0_mult_gen_v12_0_12 : entity is 1;
  attribute C_A_WIDTH : integer;
  attribute C_A_WIDTH of mult_gen_0_mult_gen_v12_0_12 : entity is 16;
  attribute C_B_TYPE : integer;
  attribute C_B_TYPE of mult_gen_0_mult_gen_v12_0_12 : entity is 1;
  attribute C_B_VALUE : string;
  attribute C_B_VALUE of mult_gen_0_mult_gen_v12_0_12 : entity is "10010010101011100";
  attribute C_B_WIDTH : integer;
  attribute C_B_WIDTH of mult_gen_0_mult_gen_v12_0_12 : entity is 17;
  attribute C_CCM_IMP : integer;
  attribute C_CCM_IMP of mult_gen_0_mult_gen_v12_0_12 : entity is 2;
  attribute C_CE_OVERRIDES_SCLR : integer;
  attribute C_CE_OVERRIDES_SCLR of mult_gen_0_mult_gen_v12_0_12 : entity is 0;
  attribute C_HAS_CE : integer;
  attribute C_HAS_CE of mult_gen_0_mult_gen_v12_0_12 : entity is 0;
  attribute C_HAS_SCLR : integer;
  attribute C_HAS_SCLR of mult_gen_0_mult_gen_v12_0_12 : entity is 0;
  attribute C_HAS_ZERO_DETECT : integer;
  attribute C_HAS_ZERO_DETECT of mult_gen_0_mult_gen_v12_0_12 : entity is 0;
  attribute C_LATENCY : integer;
  attribute C_LATENCY of mult_gen_0_mult_gen_v12_0_12 : entity is 1;
  attribute C_MODEL_TYPE : integer;
  attribute C_MODEL_TYPE of mult_gen_0_mult_gen_v12_0_12 : entity is 0;
  attribute C_MULT_TYPE : integer;
  attribute C_MULT_TYPE of mult_gen_0_mult_gen_v12_0_12 : entity is 2;
  attribute C_OPTIMIZE_GOAL : integer;
  attribute C_OPTIMIZE_GOAL of mult_gen_0_mult_gen_v12_0_12 : entity is 1;
  attribute C_OUT_HIGH : integer;
  attribute C_OUT_HIGH of mult_gen_0_mult_gen_v12_0_12 : entity is 32;
  attribute C_OUT_LOW : integer;
  attribute C_OUT_LOW of mult_gen_0_mult_gen_v12_0_12 : entity is 0;
  attribute C_ROUND_OUTPUT : integer;
  attribute C_ROUND_OUTPUT of mult_gen_0_mult_gen_v12_0_12 : entity is 0;
  attribute C_ROUND_PT : integer;
  attribute C_ROUND_PT of mult_gen_0_mult_gen_v12_0_12 : entity is 0;
  attribute C_VERBOSITY : integer;
  attribute C_VERBOSITY of mult_gen_0_mult_gen_v12_0_12 : entity is 0;
  attribute C_XDEVICEFAMILY : string;
  attribute C_XDEVICEFAMILY of mult_gen_0_mult_gen_v12_0_12 : entity is "artix7";
  attribute ORIG_REF_NAME : string;
  attribute ORIG_REF_NAME of mult_gen_0_mult_gen_v12_0_12 : entity is "mult_gen_v12_0_12";
  attribute downgradeipidentifiedwarnings : string;
  attribute downgradeipidentifiedwarnings of mult_gen_0_mult_gen_v12_0_12 : entity is "yes";
end mult_gen_0_mult_gen_v12_0_12;

architecture STRUCTURE of mult_gen_0_mult_gen_v12_0_12 is
  signal \<const0>\ : STD_LOGIC;
  signal \^p\ : STD_LOGIC_VECTOR ( 32 downto 2 );
  signal NLW_i_mult_P_UNCONNECTED : STD_LOGIC_VECTOR ( 1 downto 0 );
  signal NLW_i_mult_PCASC_UNCONNECTED : STD_LOGIC_VECTOR ( 47 downto 0 );
  signal NLW_i_mult_ZERO_DETECT_UNCONNECTED : STD_LOGIC_VECTOR ( 1 downto 0 );
  attribute C_A_TYPE of i_mult : label is 1;
  attribute C_A_WIDTH of i_mult : label is 16;
  attribute C_B_TYPE of i_mult : label is 1;
  attribute C_B_VALUE of i_mult : label is "10010010101011100";
  attribute C_B_WIDTH of i_mult : label is 17;
  attribute C_CCM_IMP of i_mult : label is 2;
  attribute C_CE_OVERRIDES_SCLR of i_mult : label is 0;
  attribute C_HAS_CE of i_mult : label is 0;
  attribute C_HAS_SCLR of i_mult : label is 0;
  attribute C_HAS_ZERO_DETECT of i_mult : label is 0;
  attribute C_LATENCY of i_mult : label is 1;
  attribute C_MODEL_TYPE of i_mult : label is 0;
  attribute C_MULT_TYPE of i_mult : label is 2;
  attribute C_OPTIMIZE_GOAL of i_mult : label is 1;
  attribute C_OUT_HIGH of i_mult : label is 32;
  attribute C_OUT_LOW of i_mult : label is 0;
  attribute C_ROUND_OUTPUT of i_mult : label is 0;
  attribute C_ROUND_PT of i_mult : label is 0;
  attribute C_VERBOSITY of i_mult : label is 0;
  attribute C_XDEVICEFAMILY of i_mult : label is "artix7";
  attribute downgradeipidentifiedwarnings of i_mult : label is "yes";
begin
  P(32 downto 2) <= \^p\(32 downto 2);
  P(1) <= \<const0>\;
  P(0) <= \<const0>\;
  PCASC(47) <= \<const0>\;
  PCASC(46) <= \<const0>\;
  PCASC(45) <= \<const0>\;
  PCASC(44) <= \<const0>\;
  PCASC(43) <= \<const0>\;
  PCASC(42) <= \<const0>\;
  PCASC(41) <= \<const0>\;
  PCASC(40) <= \<const0>\;
  PCASC(39) <= \<const0>\;
  PCASC(38) <= \<const0>\;
  PCASC(37) <= \<const0>\;
  PCASC(36) <= \<const0>\;
  PCASC(35) <= \<const0>\;
  PCASC(34) <= \<const0>\;
  PCASC(33) <= \<const0>\;
  PCASC(32) <= \<const0>\;
  PCASC(31) <= \<const0>\;
  PCASC(30) <= \<const0>\;
  PCASC(29) <= \<const0>\;
  PCASC(28) <= \<const0>\;
  PCASC(27) <= \<const0>\;
  PCASC(26) <= \<const0>\;
  PCASC(25) <= \<const0>\;
  PCASC(24) <= \<const0>\;
  PCASC(23) <= \<const0>\;
  PCASC(22) <= \<const0>\;
  PCASC(21) <= \<const0>\;
  PCASC(20) <= \<const0>\;
  PCASC(19) <= \<const0>\;
  PCASC(18) <= \<const0>\;
  PCASC(17) <= \<const0>\;
  PCASC(16) <= \<const0>\;
  PCASC(15) <= \<const0>\;
  PCASC(14) <= \<const0>\;
  PCASC(13) <= \<const0>\;
  PCASC(12) <= \<const0>\;
  PCASC(11) <= \<const0>\;
  PCASC(10) <= \<const0>\;
  PCASC(9) <= \<const0>\;
  PCASC(8) <= \<const0>\;
  PCASC(7) <= \<const0>\;
  PCASC(6) <= \<const0>\;
  PCASC(5) <= \<const0>\;
  PCASC(4) <= \<const0>\;
  PCASC(3) <= \<const0>\;
  PCASC(2) <= \<const0>\;
  PCASC(1) <= \<const0>\;
  PCASC(0) <= \<const0>\;
  ZERO_DETECT(1) <= \<const0>\;
  ZERO_DETECT(0) <= \<const0>\;
GND: unisim.vcomponents.GND
     port map (
      G => \<const0>\
    );
i_mult: entity work.mult_gen_0_mult_gen_v12_0_12_viv
     port map (
      A(15 downto 0) => A(15 downto 0),
      B(16 downto 0) => B"00000000000000000",
      CE => '0',
      CLK => CLK,
      P(32 downto 2) => \^p\(32 downto 2),
      P(1 downto 0) => NLW_i_mult_P_UNCONNECTED(1 downto 0),
      PCASC(47 downto 0) => NLW_i_mult_PCASC_UNCONNECTED(47 downto 0),
      SCLR => '0',
      ZERO_DETECT(1 downto 0) => NLW_i_mult_ZERO_DETECT_UNCONNECTED(1 downto 0)
    );
end STRUCTURE;
library IEEE;
use IEEE.STD_LOGIC_1164.ALL;
library UNISIM;
use UNISIM.VCOMPONENTS.ALL;
entity mult_gen_0 is
  port (
    CLK : in STD_LOGIC;
    A : in STD_LOGIC_VECTOR ( 15 downto 0 );
    P : out STD_LOGIC_VECTOR ( 32 downto 0 )
  );
  attribute NotValidForBitStream : boolean;
  attribute NotValidForBitStream of mult_gen_0 : entity is true;
  attribute CHECK_LICENSE_TYPE : string;
  attribute CHECK_LICENSE_TYPE of mult_gen_0 : entity is "mult_gen_0,mult_gen_v12_0_12,{}";
  attribute downgradeipidentifiedwarnings : string;
  attribute downgradeipidentifiedwarnings of mult_gen_0 : entity is "yes";
  attribute x_core_info : string;
  attribute x_core_info of mult_gen_0 : entity is "mult_gen_v12_0_12,Vivado 2017.1";
end mult_gen_0;

architecture STRUCTURE of mult_gen_0 is
  signal NLW_U0_PCASC_UNCONNECTED : STD_LOGIC_VECTOR ( 47 downto 0 );
  signal NLW_U0_ZERO_DETECT_UNCONNECTED : STD_LOGIC_VECTOR ( 1 downto 0 );
  attribute C_A_TYPE : integer;
  attribute C_A_TYPE of U0 : label is 1;
  attribute C_A_WIDTH : integer;
  attribute C_A_WIDTH of U0 : label is 16;
  attribute C_B_TYPE : integer;
  attribute C_B_TYPE of U0 : label is 1;
  attribute C_B_VALUE : string;
  attribute C_B_VALUE of U0 : label is "10010010101011100";
  attribute C_B_WIDTH : integer;
  attribute C_B_WIDTH of U0 : label is 17;
  attribute C_CCM_IMP : integer;
  attribute C_CCM_IMP of U0 : label is 2;
  attribute C_CE_OVERRIDES_SCLR : integer;
  attribute C_CE_OVERRIDES_SCLR of U0 : label is 0;
  attribute C_HAS_CE : integer;
  attribute C_HAS_CE of U0 : label is 0;
  attribute C_HAS_SCLR : integer;
  attribute C_HAS_SCLR of U0 : label is 0;
  attribute C_HAS_ZERO_DETECT : integer;
  attribute C_HAS_ZERO_DETECT of U0 : label is 0;
  attribute C_LATENCY : integer;
  attribute C_LATENCY of U0 : label is 1;
  attribute C_MODEL_TYPE : integer;
  attribute C_MODEL_TYPE of U0 : label is 0;
  attribute C_MULT_TYPE : integer;
  attribute C_MULT_TYPE of U0 : label is 2;
  attribute C_OPTIMIZE_GOAL : integer;
  attribute C_OPTIMIZE_GOAL of U0 : label is 1;
  attribute C_OUT_HIGH : integer;
  attribute C_OUT_HIGH of U0 : label is 32;
  attribute C_OUT_LOW : integer;
  attribute C_OUT_LOW of U0 : label is 0;
  attribute C_ROUND_OUTPUT : integer;
  attribute C_ROUND_OUTPUT of U0 : label is 0;
  attribute C_ROUND_PT : integer;
  attribute C_ROUND_PT of U0 : label is 0;
  attribute C_VERBOSITY : integer;
  attribute C_VERBOSITY of U0 : label is 0;
  attribute C_XDEVICEFAMILY : string;
  attribute C_XDEVICEFAMILY of U0 : label is "artix7";
  attribute downgradeipidentifiedwarnings of U0 : label is "yes";
begin
U0: entity work.mult_gen_0_mult_gen_v12_0_12
     port map (
      A(15 downto 0) => A(15 downto 0),
      B(16 downto 0) => B"00000000000000000",
      CE => '1',
      CLK => CLK,
      P(32 downto 0) => P(32 downto 0),
      PCASC(47 downto 0) => NLW_U0_PCASC_UNCONNECTED(47 downto 0),
      SCLR => '0',
      ZERO_DETECT(1 downto 0) => NLW_U0_ZERO_DETECT_UNCONNECTED(1 downto 0)
    );
end STRUCTURE;
