janelia-experimental-technology/FlySong/PHOTOS/back of cameras.jpg

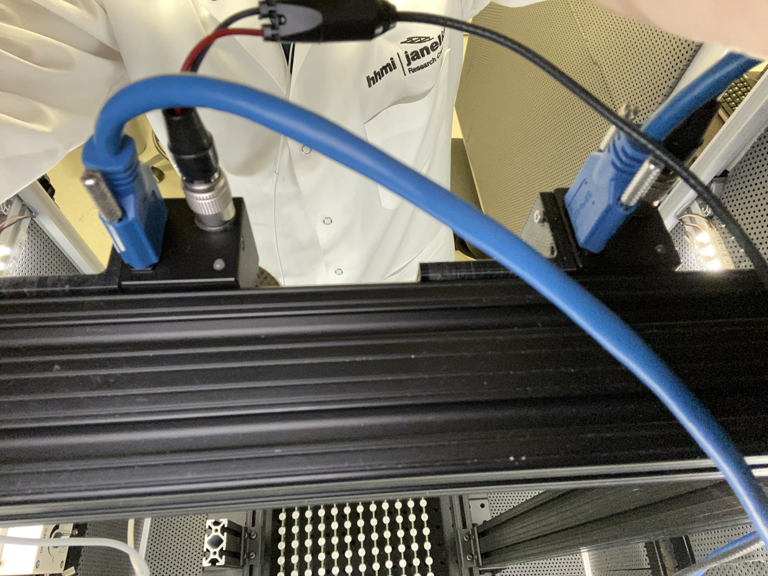
PHOTOS/back of cameras.jpg
